Nikolaossamaras/marinboard/image-4.png

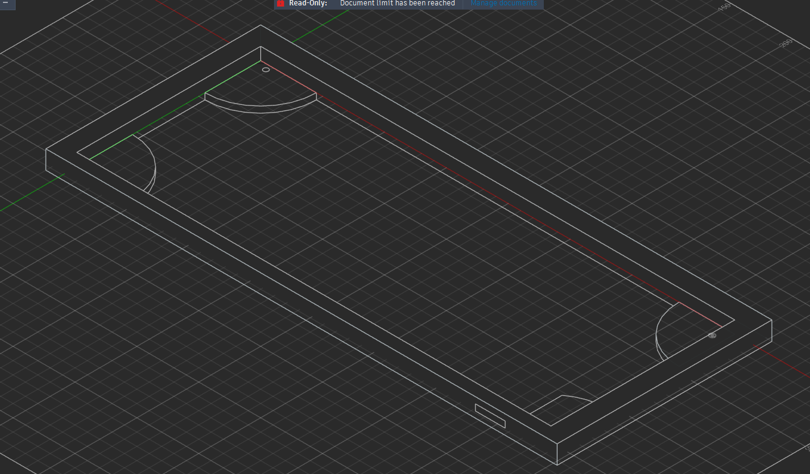
image-4.png
